embodied-computation-group/RespiroceptionMethodsPaper/figs/figure_8.png

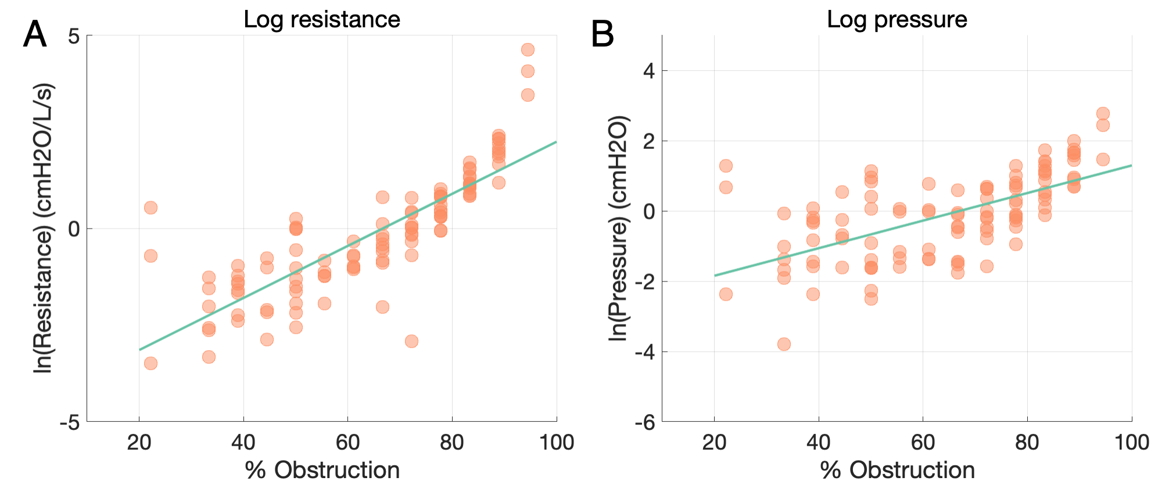
figs/figure_8.png
