embodied-computation-group/RespiroceptionMethodsPaper/figs/graphicalAbstract_revision.png

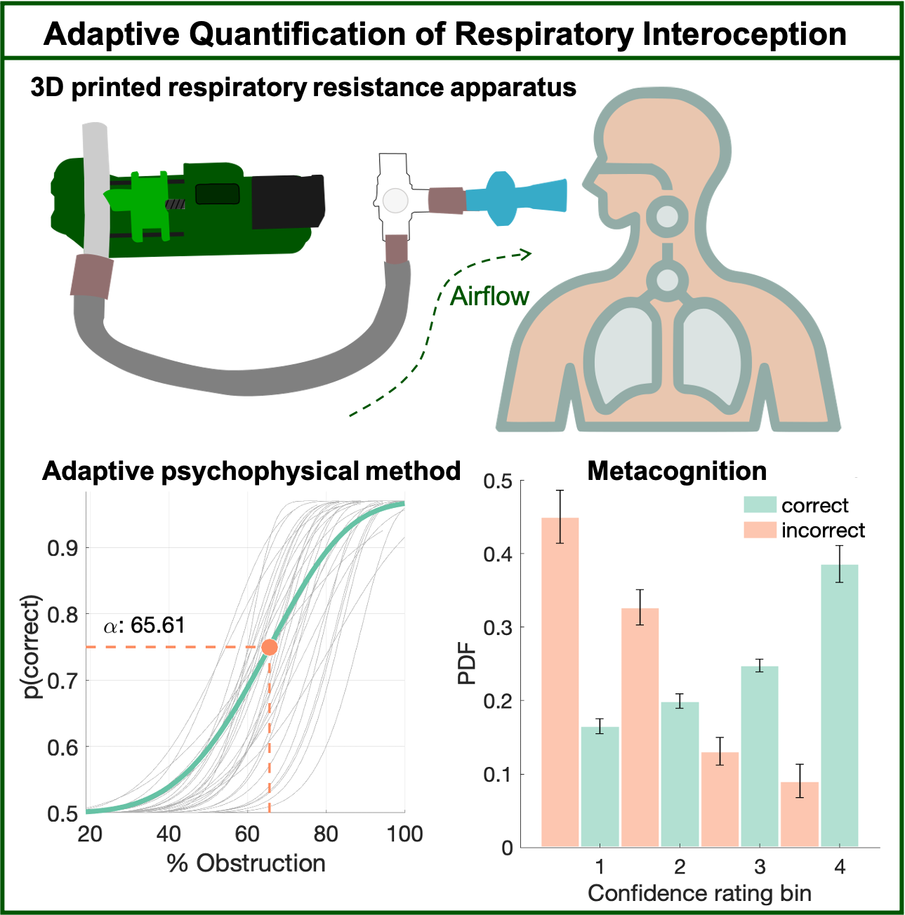
figs/graphicalAbstract_revision.png
