embodied-computation-group/RespiroceptionMethodsPaper/figs/RRST_devicePhoto.png

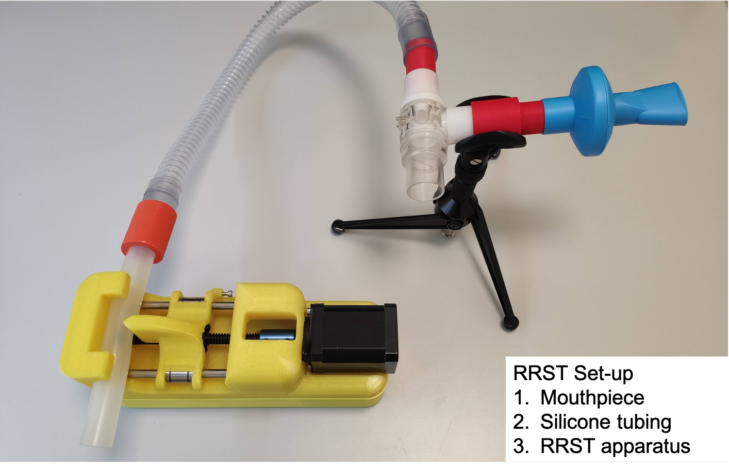
figs/RRST_devicePhoto.png
