embodied-computation-group/RespiroceptionMethodsPaper/figs/RRST_MP_suppfig_3.png

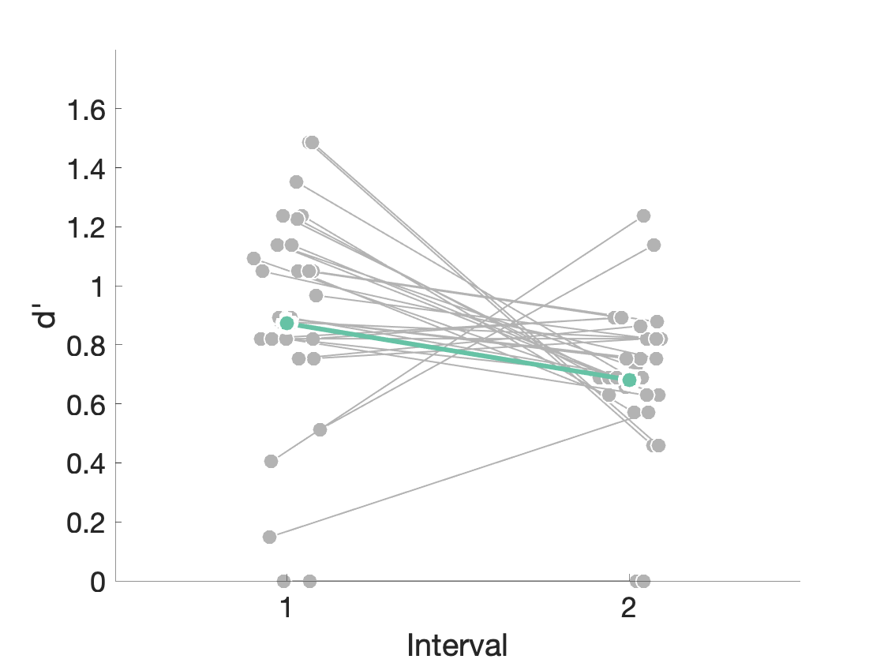
figs/RRST_MP_suppfig_3.png
