embodied-computation-group/RespiroceptionMethodsPaper/task/apparatus/version_3-0/photos/20220426_095023.jpg

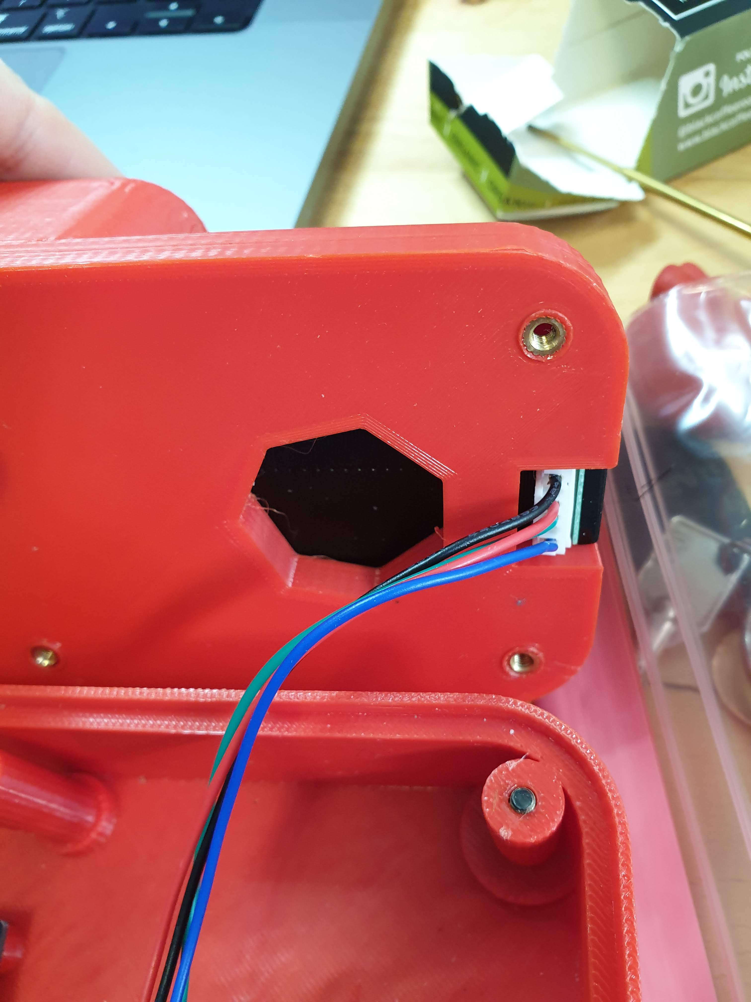
task/apparatus/version_3-0/photos/20220426_095023.jpg
