embodied-computation-group/RespiroceptionMethodsPaper/task/apparatus/version_3-0/photos/20220520_141144 (2).jpg

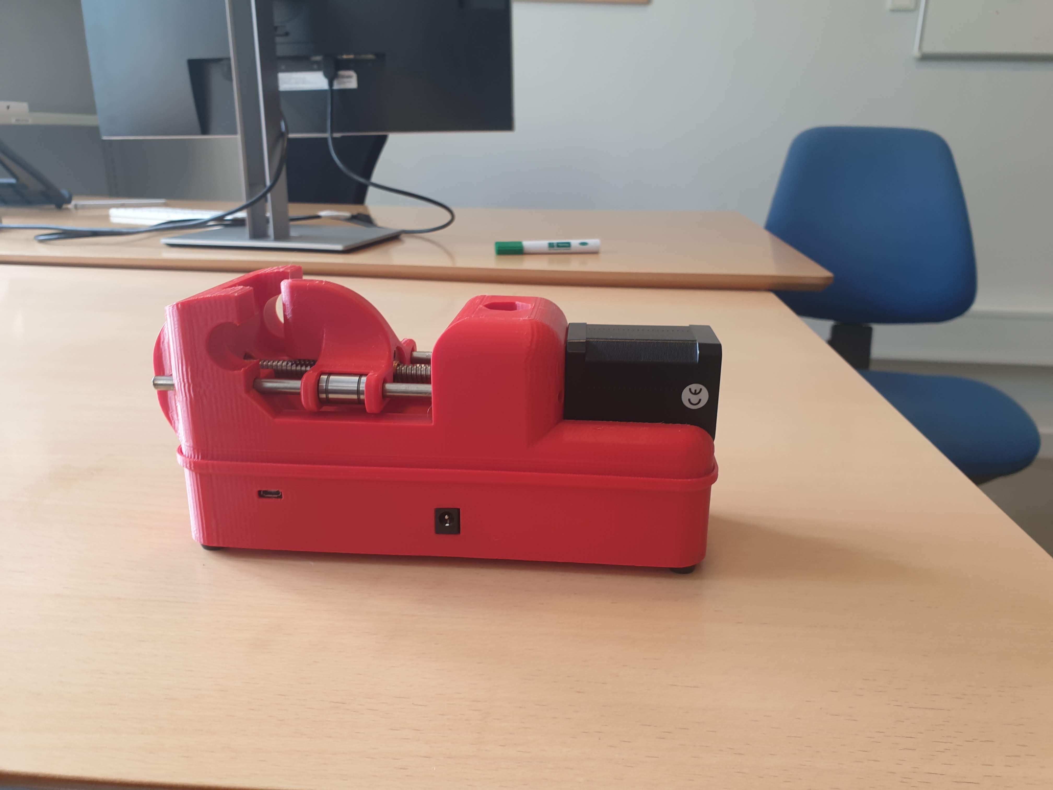
task/apparatus/version_3-0/photos/20220520_141144 (2).jpg
